ByPS128/Arduino-Aliens-M41A-Rifle/src/M41A/GranadeLedAnimator.h

#pragma once

#include <Arduino.h>

class GranadeLedAnimator {
public:
    void setup(int granadePwmLedPin, int timeToFullFadeOutInMs);
    void update();
    void start();
    void stop();

private:
    int ledPin;
    int fadeOutTime;
    unsigned long startTime;
    bool isAnimating;

private:
    void ledOff();
};
