ByPS128/Arduino-Aliens-M41A-Rifle/src/M41A/M41aPlayer.h

#pragma once

#include <Arduino.h>
#include "AppConstants.h"
#include "DFPlay.h"

class M41aPlayer {
private:
  DFPlay dfPlay;
  int lastFireInstrument;
  int lastEmptyMagazineInstrument;
  unsigned long explosionTime = 0; // Randomly calculated time in milliveterin for how long it takes for the grenade to explode
  bool explosionScheduled = false; // Flag if the explosion is planned (if the grenade was fired)

private:
  volatile int volume = 20;

public:
  M41aPlayer();
  void setup(byte newVolume);
  void update();

public:
  bool getPlaying();
  byte getVolume();
  void setVolume(byte newVolume);
  void volumeIncrement();
  void volumeDecrement();
  void stop();
  void setEqualizer(byte equalizerType);

public:
  void resetGranadeExplositon();
  void playRifleFire(int bulletsCount);
  void playCock();
  void playMagazineReload();
  void playMagazineEject();
  void playMagazineLoad();
  void playEmptyMagazine();
  void playClick();
  void playVolumeSaved();
  void playVolumeUp();
  void playVolumeDown();
  void playCardInserted();
  void playCardRemoved();
  void playLowBattery();
  void playWeaponReady();
  void playGranadeLoad();
  void playGranadeFire();
  void playGranadeExplosion();
};
